aghoward/bluefish-firmware/serial_stream.cpp

#include "serial_stream.h"

#include <Arduino.h>

#include "char_string.h"

void SerialStream::write(unsigned short, const char* data, unsigned long size)
{
    Serial.write(data, size);
    Serial.flush();
}

CharString SerialStream::read(unsigned short, unsigned long size) const
{
    while (!Serial.available()) {}
    auto output = CharString(size);
    Serial.readBytes(output.data(), size);
    return output;
}
